SeAMKedu/sebot/code/md-publisher/markdown_files/materiaali-1-lowlevel.md

## Moottorinohjaus

### Yleiskuvaus

ohjain ja moottorit

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

Tämä laskenta edellyttää seuraavia tietoja:

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

**DC-moottorin ohjaus ja Arduino:**

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

Ohjelma määrittää moottorin pyörimissuunnan PID-säätimen tai PWM-komennon tuottaman arvon perusteella:

- Positiivinen arvo ohjaa moottorin pyörimään eteenpäin.
- Negatiivinen arvo kääntää moottorin suunnan taaksepäin.

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

### Laitteisto

ohjain ja moottorit

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

### Kytkentä

Allaolevassa taulukossa on selvitetty kytkennät Arduino Micron, L293D piirin ja moottoreiden välillä.

 <table>
<tr>
<td valign="top">
<strong>MOOTTORIN JOHTOJEN KYTKENNÄT</strong>

| moottori johdin  | toiminta  | kohde  | nasta |
|---|---|---|---|
| valkoinen | motor - | L293D | M#1->3, M#2->11 |
| sininen | sensor + | Arduino  | +5V |
| vihreä | A | Arduino  | M#1->3, M#2->2  |
| keltainen | B | Arduino  | M#1->4, M#2->9  |
| musta | sensor gnd | Arduino  | gnd |
| punainen  | motor + | L293D | M#1->6, M#2->14 |

 Arduino Micron kytkennät. Punaiset ympyröinnit osoittavat käytössä olevat nastat.

</td><td>
<strong>H-SILTA L293D KYTKENNÄT</strong>

| L293D nasta| toiminta | kohde |  nasta / johdin |
|---|---|---|---|
| 1 | enable1 | Arduino | 5 |
| 2 | input1 | Arduino | 6 |
| 3 | output1 | Moottori #1 | valkoinen |
| 4 | gnd | Arduino | gnd |
| 5 | gnd | Arduino | gnd |
| 6 | output2 | Moottori #1 | punainen |
| 7 | input2 | Arduino | 8 |
| 8 | Vs | Akku | +12V (ajojännite) |
| 9 | enable2 | Arduino | 10 |
| 10 | input3 | Arduino | 11 |
| 11 | output3 | Moottori #2 | valkoinen |
| 12 | gnd | Arduino | gnd |
| 13 | gnd | Arduino | gnd |
| 14 | output4 | Moottori #2 | punainen |
| 15 | input4 | Arduino | 12 |
| 16 | Vss. | Arduino | +5V |

</td>
</tr>
</table>

#### Komennot
Arduinoon on ohjelmoitu seuraavat komennot:

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

Kaikki komennot palauttavat stringin:  ``encoder1;encoder2;rpm1;rpm2;pwm1;pwm2``

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

https://docs.arduino.cc/learn/microcontrollers/analog-output/

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

**pwm.py**

```python
import serial
import time

try:
    speed = 100
    arduino = serial.Serial("/dev/ttyACM0", 115200, timeout=1)
    time.sleep(2.0) # odotetaan etta linja on varmasti auki
    arduino.write(("PWM;%s;%s;\n"%(speed,speed)).encode()) #annetaan pwm ohje kummallekin moottorille
    if arduino.isOpen():
        while(True):
            print("Moottorit pyorivat yha")
            time.sleep(3.0)
            
except KeyboardInterrupt:
        print("\nOhjelma keskeytetty, pysaytetaan moottorit.")
        arduino.write(("PWM;0;0").encode())
        
finally:
        print("Lopetetaan ohjelma")
```

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

```bash
# Ajetaan ohjelma komennolla
python3 pwm.py
```
##### Jos mitään ei tapahdu, tarkista seuraavat asiat:

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

### Takaisinkytkentä

Teemme koodiin pienen lisäyksen, jonka avulla tulostamme moottoriohjaimelta saadun vastauksen. Vastaus saapuu muodossa:

```motor1_encoder;motor2_encoder;motor1_speed;motor2_speed;motor1_pwm_set;motor2_pwm_set```

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

```python
import serial
import time
import random
try:

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

            if arduino.inWaiting()>0:
                answer=arduino.readline()
                print(answer)
                arduino.flushInput()
            
except KeyboardInterrupt:
        print("\nOhjelma keskeytetty, pysaytetaan moottorit.")
        arduino.write(("PWM;0;0").encode())
        
finally:
        print("Lopetetaan ohjelma")
```

Ja kun ajamme ohjelman, saamme vastauksia

```
python pwm.py

b'-552;-518;169;158;100;100\n'
b'-1324;-1237;179;166;100;100\n'
b'-2103;-1963;179;167;100;100\n'
b'-2884;-2692;180;168;100;100\n'
b'-3666;-3422;181;168;100;100\n'
b'-4449;-4154;180;168;100;100\n'
b'-5233;-4887;180;169;100;100\n'
b'-6018;-5621;181;169;100;100\n'
b'-6802;-6356;181;170;100;100\n'
b'-7588;-7093;181;170;100;100\n'
b'-8372;-7828;181;170;100;100\n'
b'-9158;-8564;181;169;100;100\n'
b'-9946;-9300;181;169;100;100\n'
b'-10735;-10037;181;169;100;100\n'
b'-11523;-10772;182;169;100;100\n'
b'-12312;-11508;182;169;100;100\n'
b'-13102;-12245;182;170;100;100\n'
```

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

pwm

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

### PID Säädin

PID säätimen toimintaan voit tutustua tutustumalla arduinoissa olevaan koodiin.

pwm

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

SPD;127;127; tarkoittaa, että kumpikin moottori pyrkii pitämään nopeuden 127

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

```python
import serial
import time

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

	    if arduino.inWaiting()>0:
	      answer=arduino.readline()
	      print(answer)
	      arduino.flushInput()
	      
except KeyboardInterrupt:
	print("Pysaytetaan moottorit")
	arduino.write(("SPD;0;0").encode())
finally:
	print("Lopetetaan ohjelma")
```

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

```
b'-510;-498;141;135;20;32\n'
b'-926;-924;105;104;52;58\n'
b'-1354;-1354;101;100;57;61\n'
b'-1787;-1786;101;102;57;60\n'
b'-2216;-2216;99;99;58;62\n'
b'-2648;-2645;100;97;57;63\n'
b'-3081;-3075;101;98;57;62\n'
b'-3511;-3507;99;100;58;61\n'
b'-3945;-3939;100;100;57;62\n'
b'-4375;-4372;100;100;57;61\n'
b'-4806;-4802;99;100;58;61\n'
b'-5236;-5233;99;101;58;61\n'
b'-5668;-5665;101;100;57;61\n'
b'-6102;-6099;100;100;57;61\n'
b'-6532;-6527;100;99;57;62\n'
b'-6964;-6960;99;99;58;62\n'
b'-7399;-7393;101;99;56;61\n'
```

pwm

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

pwm

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

pwm

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

### Vaihtoehtoja

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

-
Nomga Oy - SeAMK - ROS 2 ja moottorinohjaus: PWM-signaalista robottien liikkeenhallintaan
