SeAMKedu/sebot/code/md-publisher/markdown_files/kuvat/schema.png

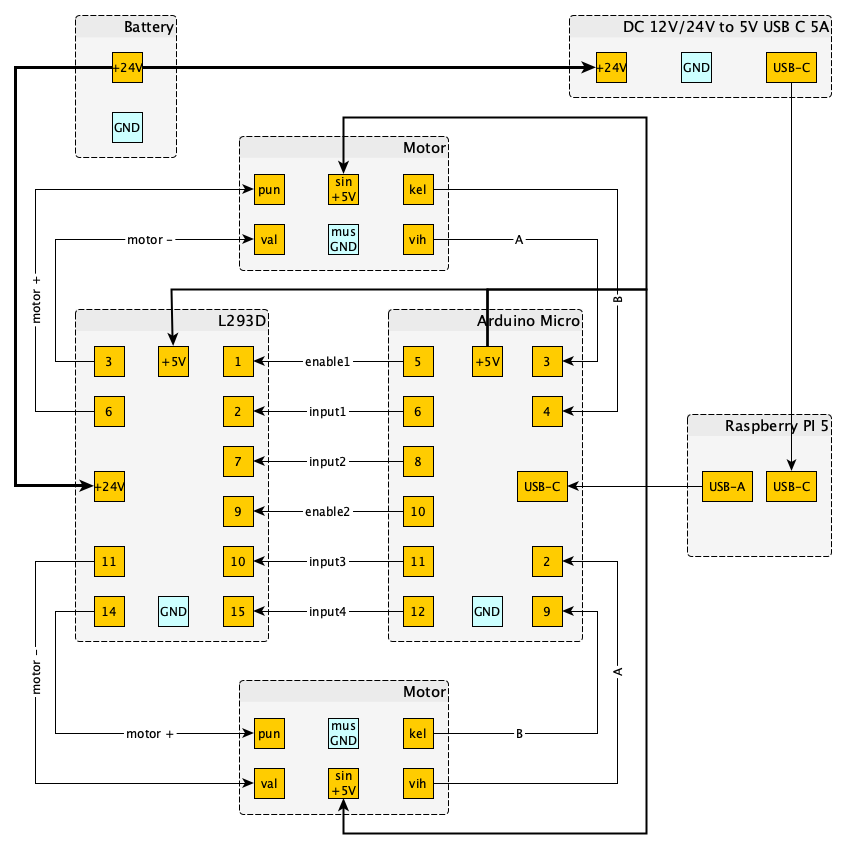
code/md-publisher/markdown_files/kuvat/schema.png
