SeAMKedu/sebot/code/md-publisher/markdown_files/kuvat/yleiskuva2.jpg

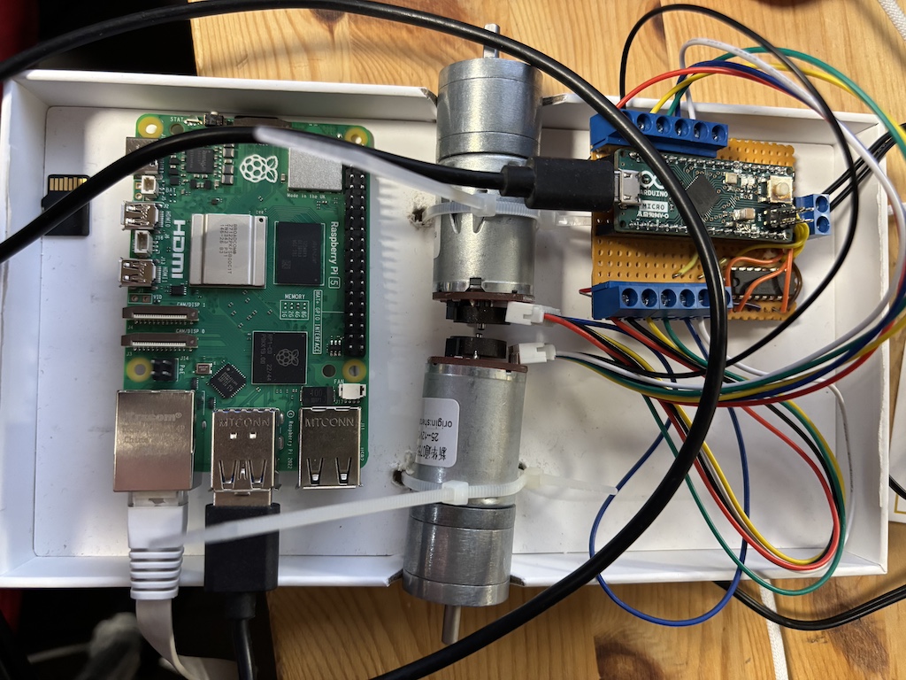
code/md-publisher/markdown_files/kuvat/yleiskuva2.jpg
